MarcEGed/Mini-Project/docs/diagrams/audio-pipe-transmit.png

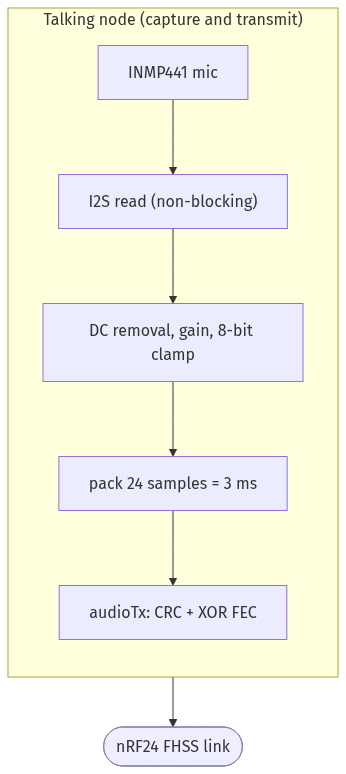
docs/diagrams/audio-pipe-transmit.png
