MarcEGed/Mini-Project/docs/diagrams/hop-timeline.png

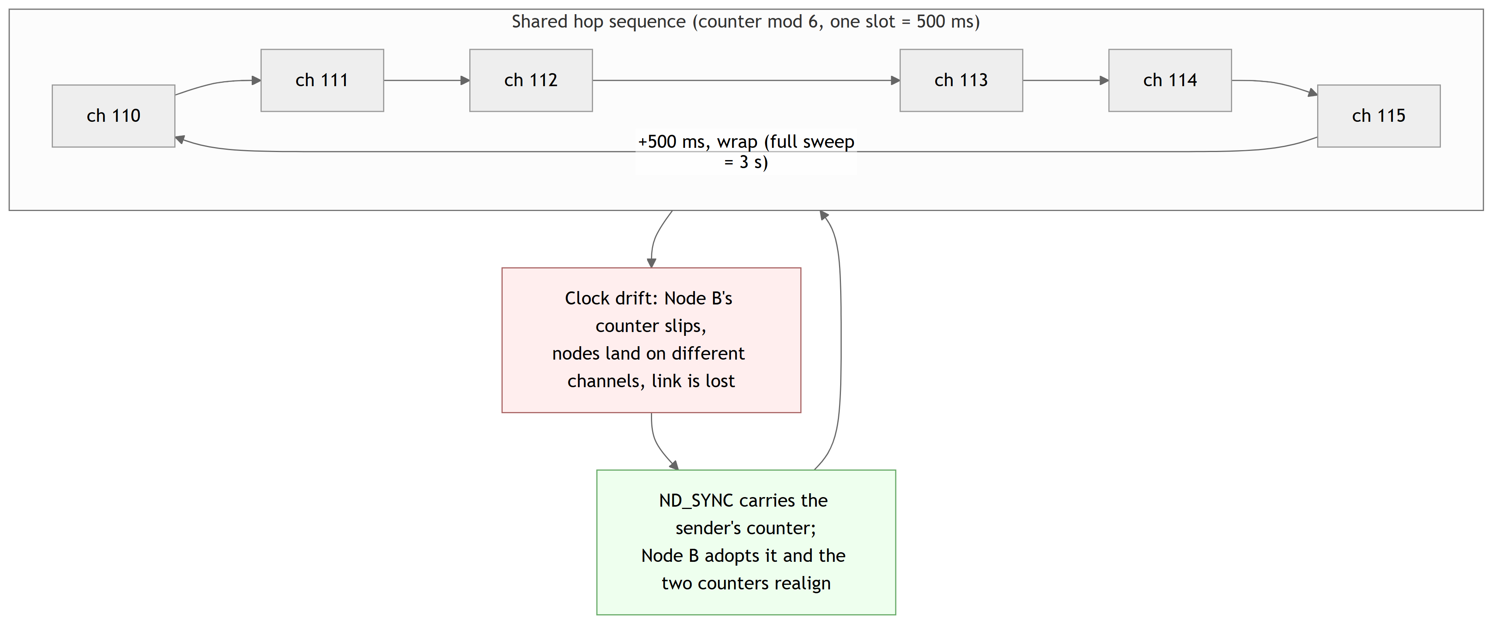
docs/diagrams/hop-timeline.png
