MarcEGed/Mini-Project/docs/diagrams/packet.png

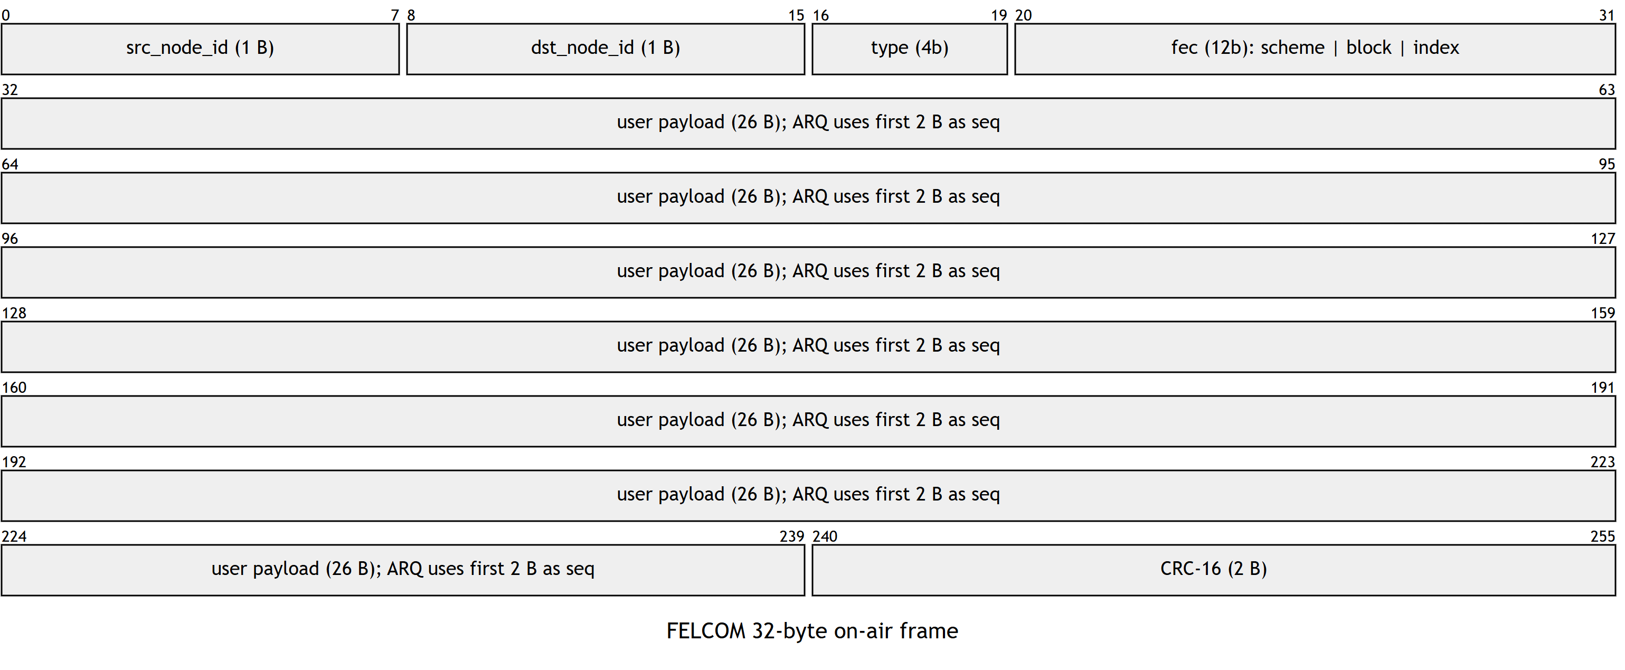
docs/diagrams/packet.png
